make-42/pScreen/CAD/Ref/image-7.png

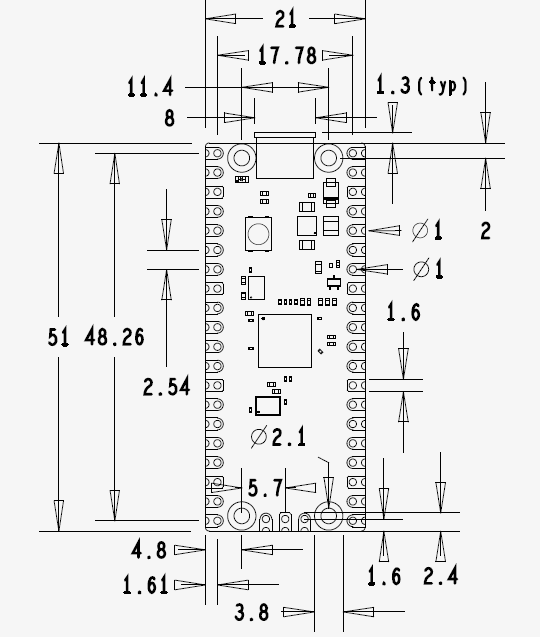
CAD/Ref/image-7.png
